TerrenceCao1/GuitarPedals/src/Effects.cpp

#include <algorithm>
#include <iostream>
#include <cmath>
#include <cinttypes>
#include "AudioFrame.h"
#include "Effects.h"

void Effects::Bypass(const AudioFrame &inFrame, AudioFrame &outFrame)
{
	const auto& in = inFrame.getData();
	auto& out = outFrame.getDataMutable();
	size_t n = inFrame.getNumSamples();

	for(size_t i = 0; i < n; i++)
		out[i] = in[i];
}

void Effects::Boost(const AudioFrame &inFrame, AudioFrame &outFrame, double gainDb)
{
	double linearGain = std::pow(10.0, gainDb / 20.0);
	const auto& in = inFrame.getData();
	auto& out = outFrame.getDataMutable();
	size_t n = inFrame.getNumSamples();

	for(size_t i = 0; i < n; i++)
	{
		out[i] = in[i] * linearGain;
	}
}

void Effects::HardClip(const AudioFrame& inFrame, AudioFrame& outFrame, double gain, double threshold)
{
	Effects::Boost(inFrame, outFrame, gain);

	auto& out = outFrame.getDataMutable();
	size_t n = inFrame.getNumSamples();

	for(size_t i = 0; i < n; i++)
	{
		out[i] = std::clamp(out[i], -threshold, threshold);
	}
}
